mloit/zbvr/docs/assets/wiring-photos/02-LED-parts-flat.jpg

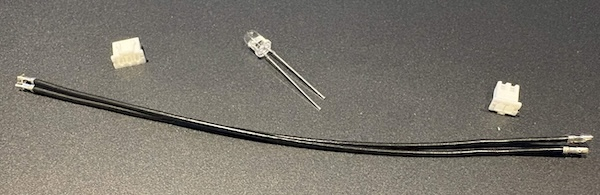
docs/assets/wiring-photos/02-LED-parts-flat.jpg
