mloit/zbvr/docs/assets/assembly-renderings/Connector Pin Numbering.png

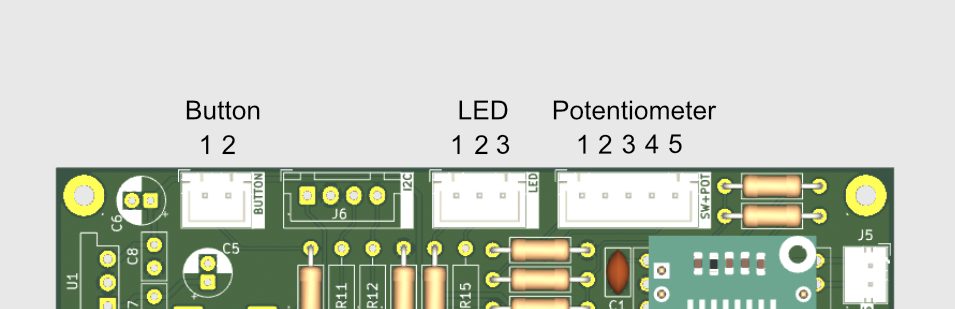
docs/assets/assembly-renderings/Connector Pin Numbering.png
