mloit/zbvr/docs/assets/wiring-photos/xx-XHP-2.jpg

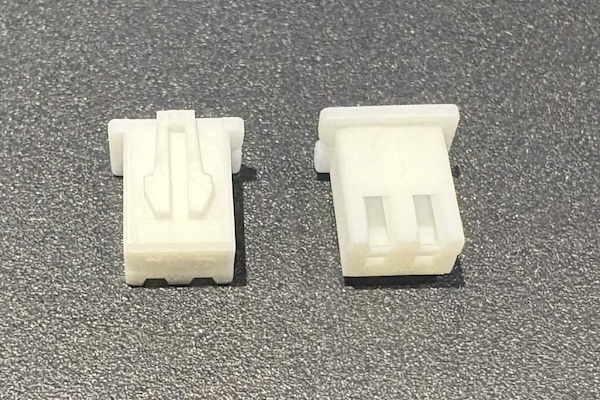
docs/assets/wiring-photos/xx-XHP-2.jpg
