mloit/zbvr/docs/assets/wiring-photos/xx-XHP-3.jpg

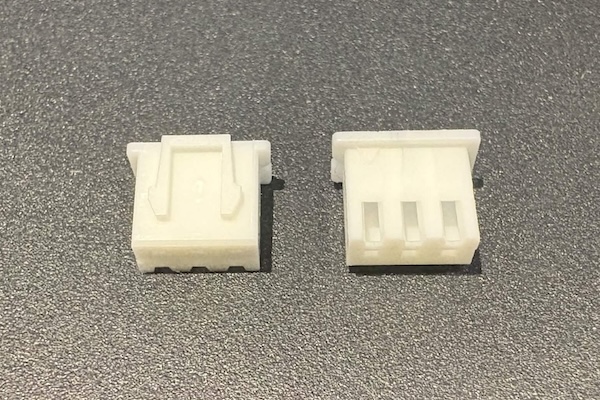
docs/assets/wiring-photos/xx-XHP-3.jpg
