mloit/zbvr/docs/assets/wiring-photos/xx-XHP-5.jpg

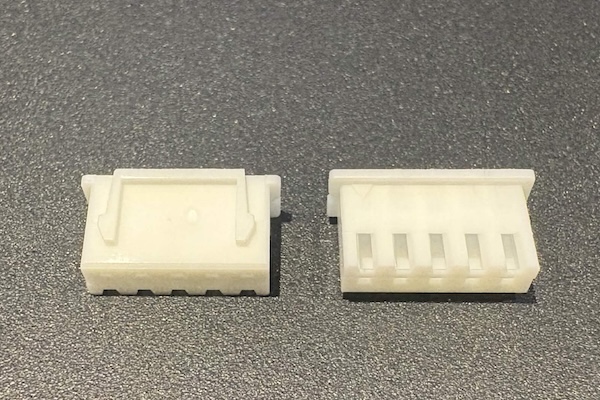
docs/assets/wiring-photos/xx-XHP-5.jpg
